1sand0s/Solder_Reflow_Oven/DSCN6111.JPG

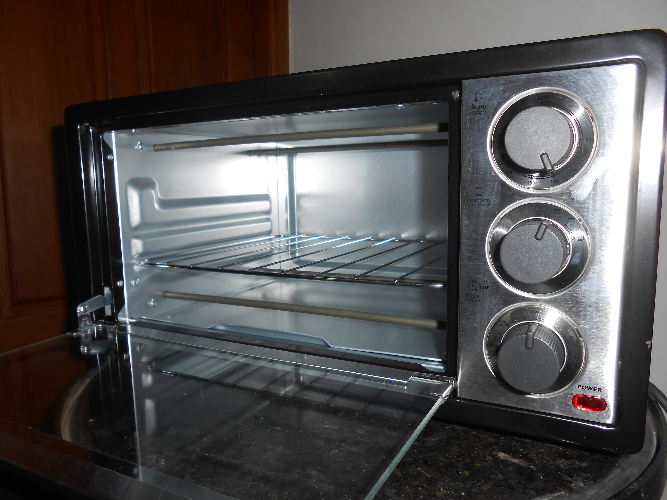
DSCN6111.JPG
